kholia/Easy-Beacons-STEM/Amplified-WSPR-Beacon-v3/info/KK81.png

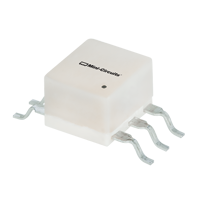
Amplified-WSPR-Beacon-v3/info/KK81.png
