kholia/Easy-Beacons-STEM/Amplified-WSPR-Beacon-v3/info/Screenshot_2022-12-17_13-03-08.png

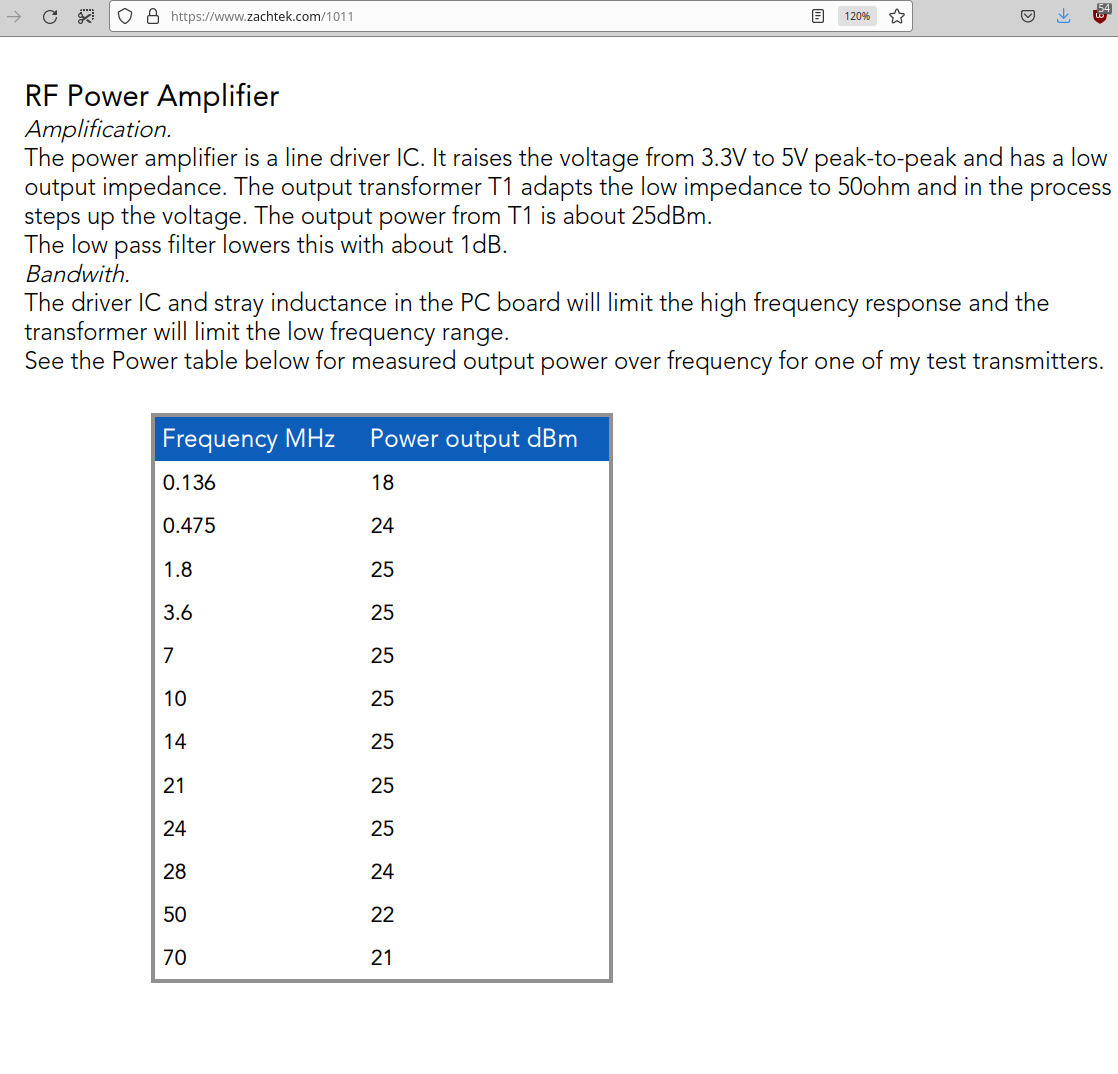
Amplified-WSPR-Beacon-v3/info/Screenshot_2022-12-17_13-03-08.png
