kholia/Easy-Beacons-STEM/Amplified-WSPR-Beacon-v3/info/Screenshot_2023-01-06_15-30-46.png

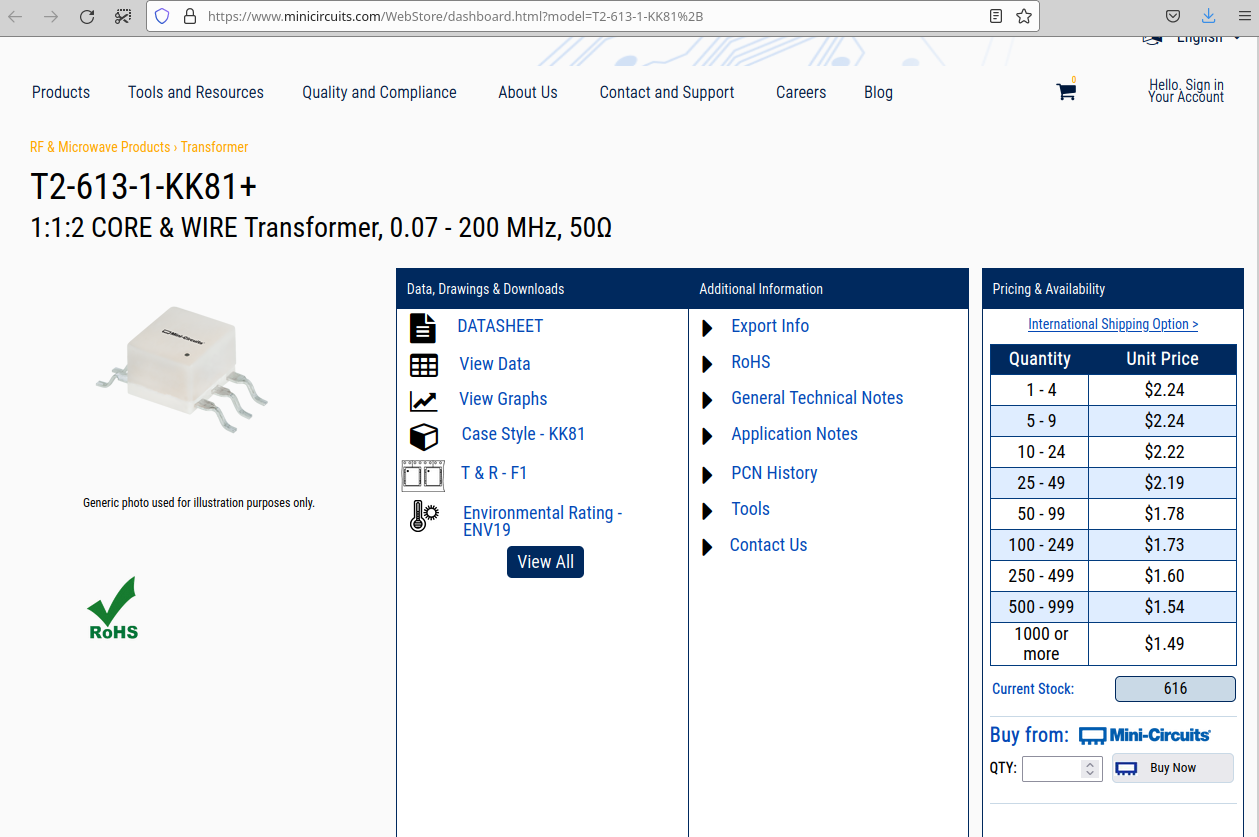
Amplified-WSPR-Beacon-v3/info/Screenshot_2023-01-06_15-30-46.png
