kholia/Easy-Beacons-STEM/Amplified-WSPR-Beacon-v3/info/WSPR Desktop Open small.jpg

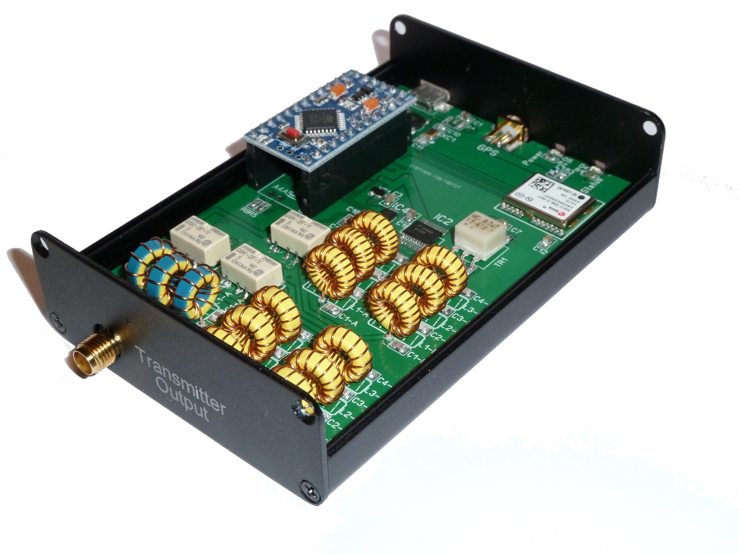
Amplified-WSPR-Beacon-v3/info/WSPR Desktop Open small.jpg
