kholia/Easy-Beacons-STEM/Amplified-WSPR-Beacon/Home-RX-Park-TX-Screenshot_2022-10-17_21-01-00.png

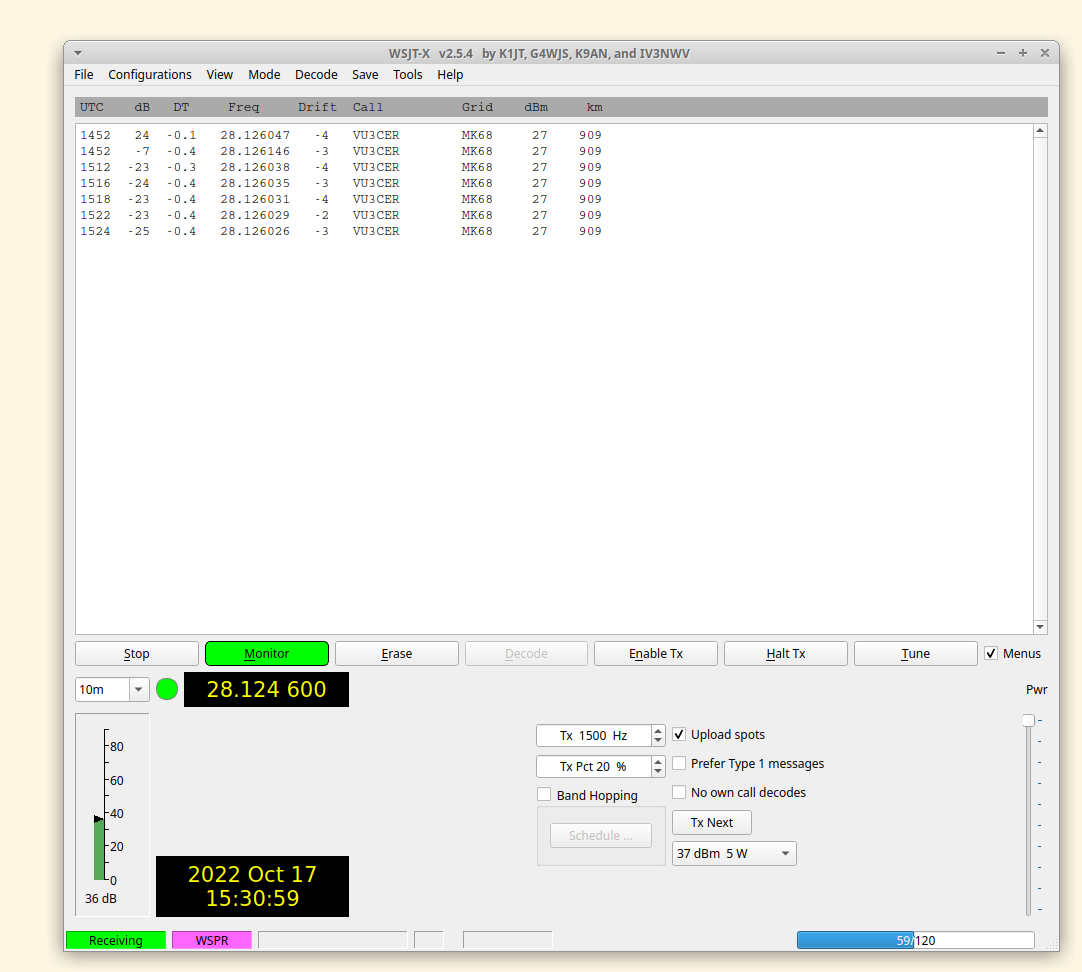
Amplified-WSPR-Beacon/Home-RX-Park-TX-Screenshot_2022-10-17_21-01-00.png
