kholia/Easy-Beacons-STEM/Amplified-WSPR-Beacon/Same-7.4v-Screenshot_2022-10-18_15-10-08.png

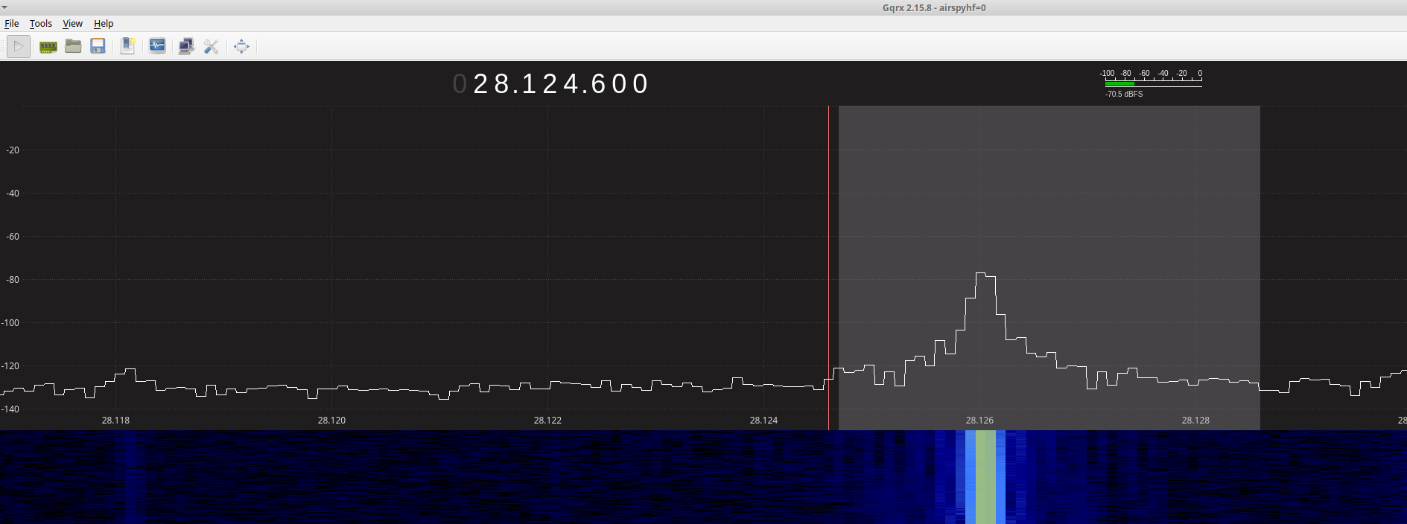
Amplified-WSPR-Beacon/Same-7.4v-Screenshot_2022-10-18_15-10-08.png
