kholia/Easy-Beacons-STEM/Amplified-WSPR-Beacon/Screenshot_2022-10-17_15-22-22.png

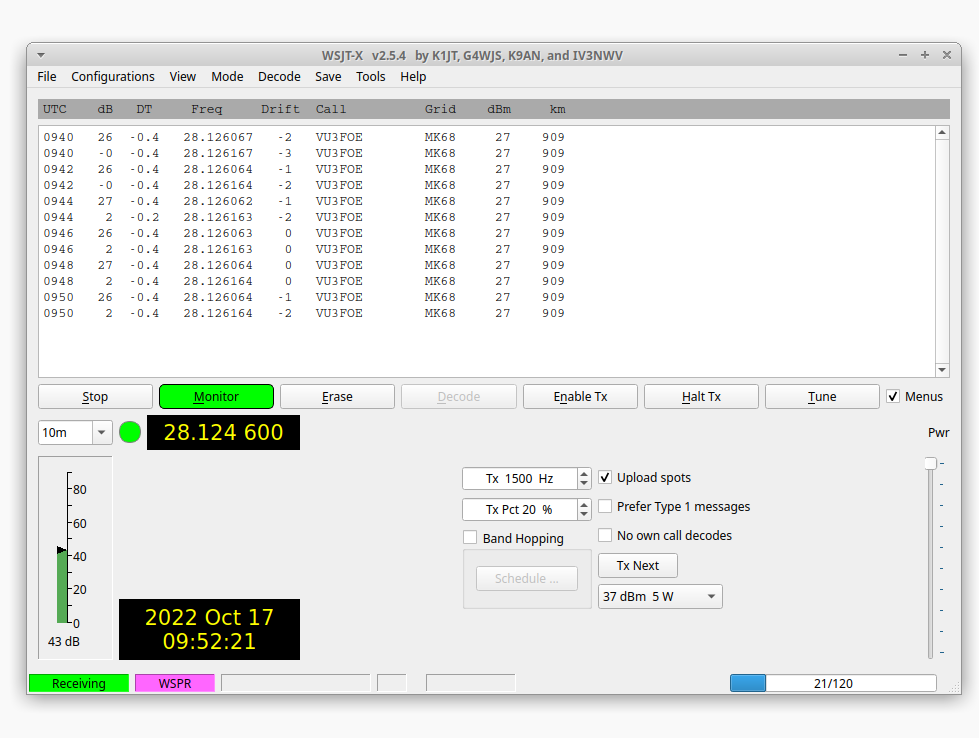
Amplified-WSPR-Beacon/Screenshot_2022-10-17_15-22-22.png
