kholia/Easy-Beacons-STEM/Amplified-WSPR-Beacon/Screenshot_2022-10-17_15-31-09.png

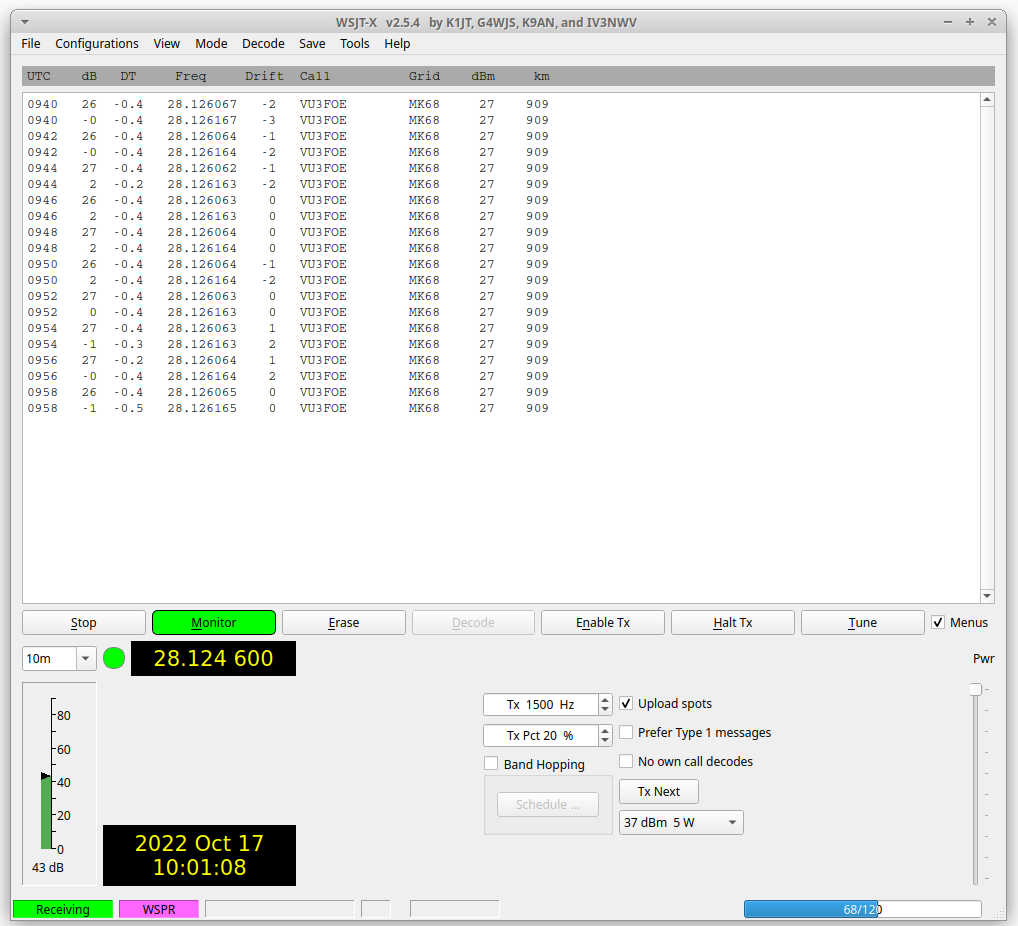
Amplified-WSPR-Beacon/Screenshot_2022-10-17_15-31-09.png
