kholia/Easy-Beacons-STEM/Amplified-WSPR-Beacon/Screenshot_2022-10-19_18-15-18.png

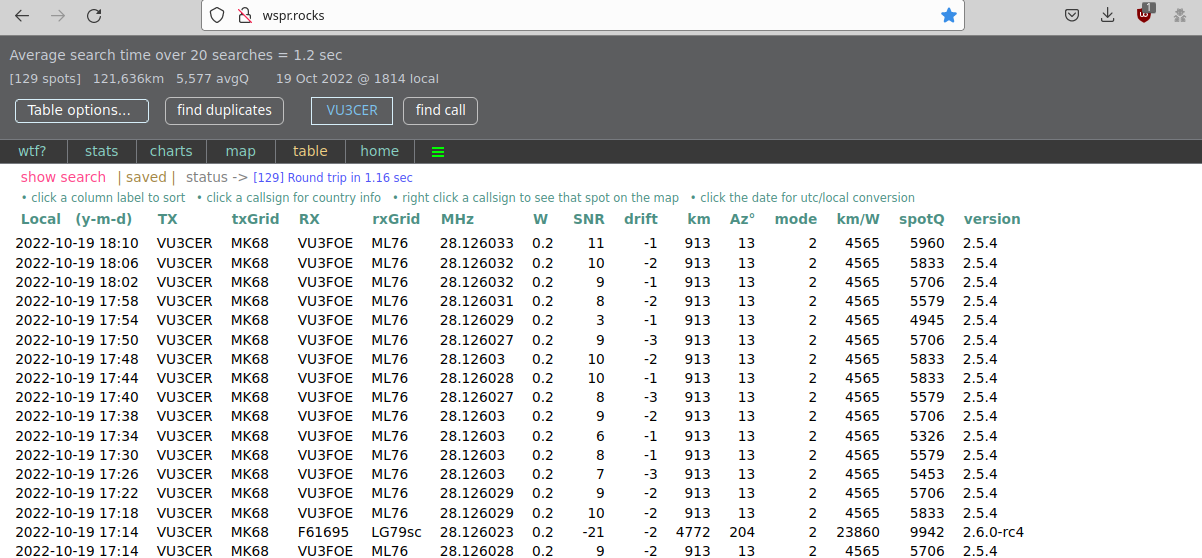
Amplified-WSPR-Beacon/Screenshot_2022-10-19_18-15-18.png
