kholia/Easy-Beacons-STEM/Amplified-WSPR-Beacon/Screenshot_2022-10-19_19-35-20.png

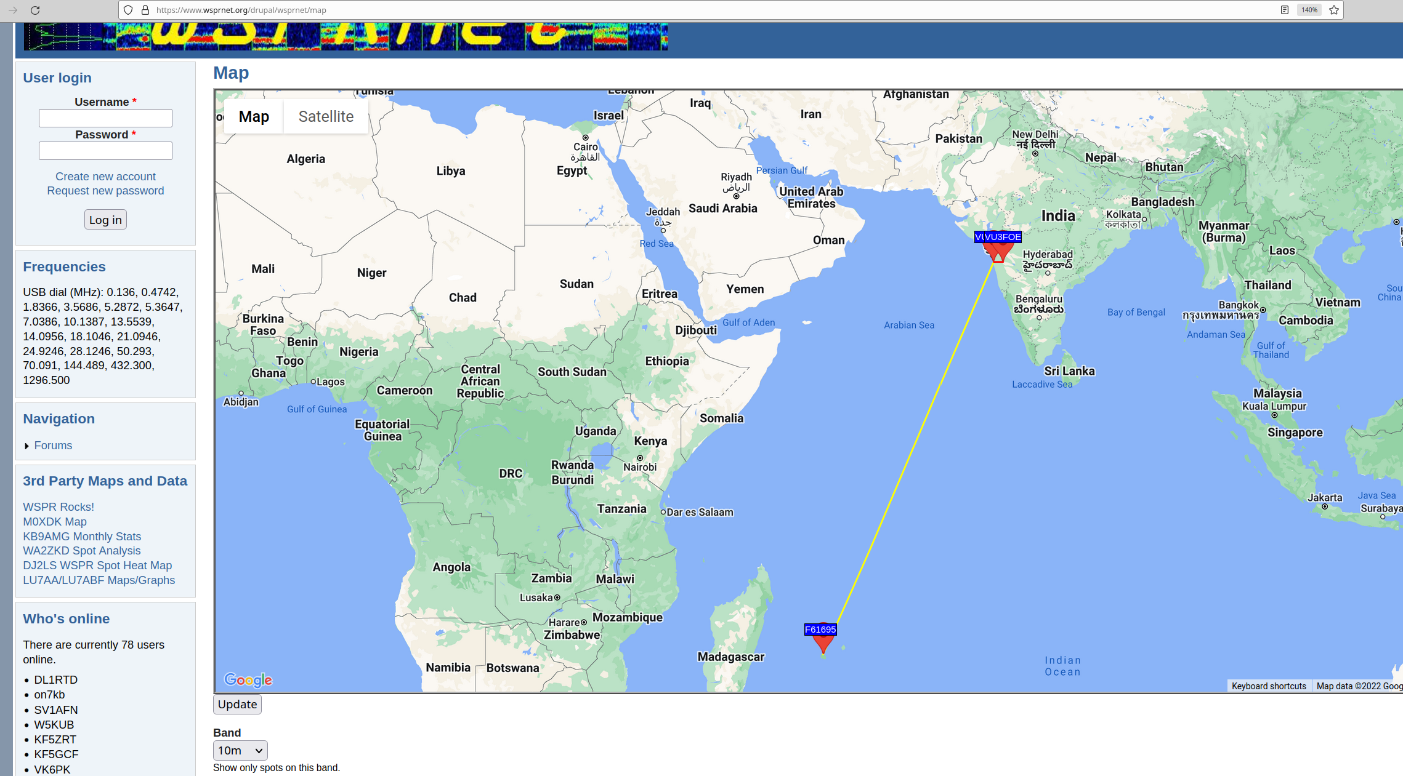
Amplified-WSPR-Beacon/Screenshot_2022-10-19_19-35-20.png
