kholia/Easy-Beacons-STEM/Amplified-WSPR-Beacon/Screenshot_2022-10-24_17-50-40.png

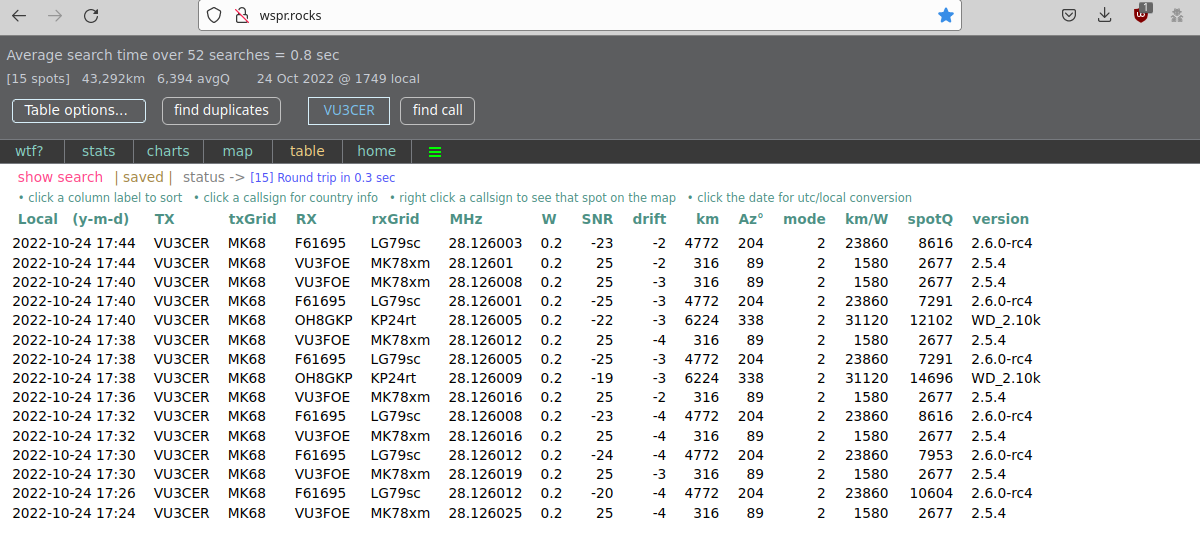
Amplified-WSPR-Beacon/Screenshot_2022-10-24_17-50-40.png
