kholia/Easy-Beacons-STEM/Amplified-WSPR-Beacon/Screenshot_2022-10-24_18-13-15.png

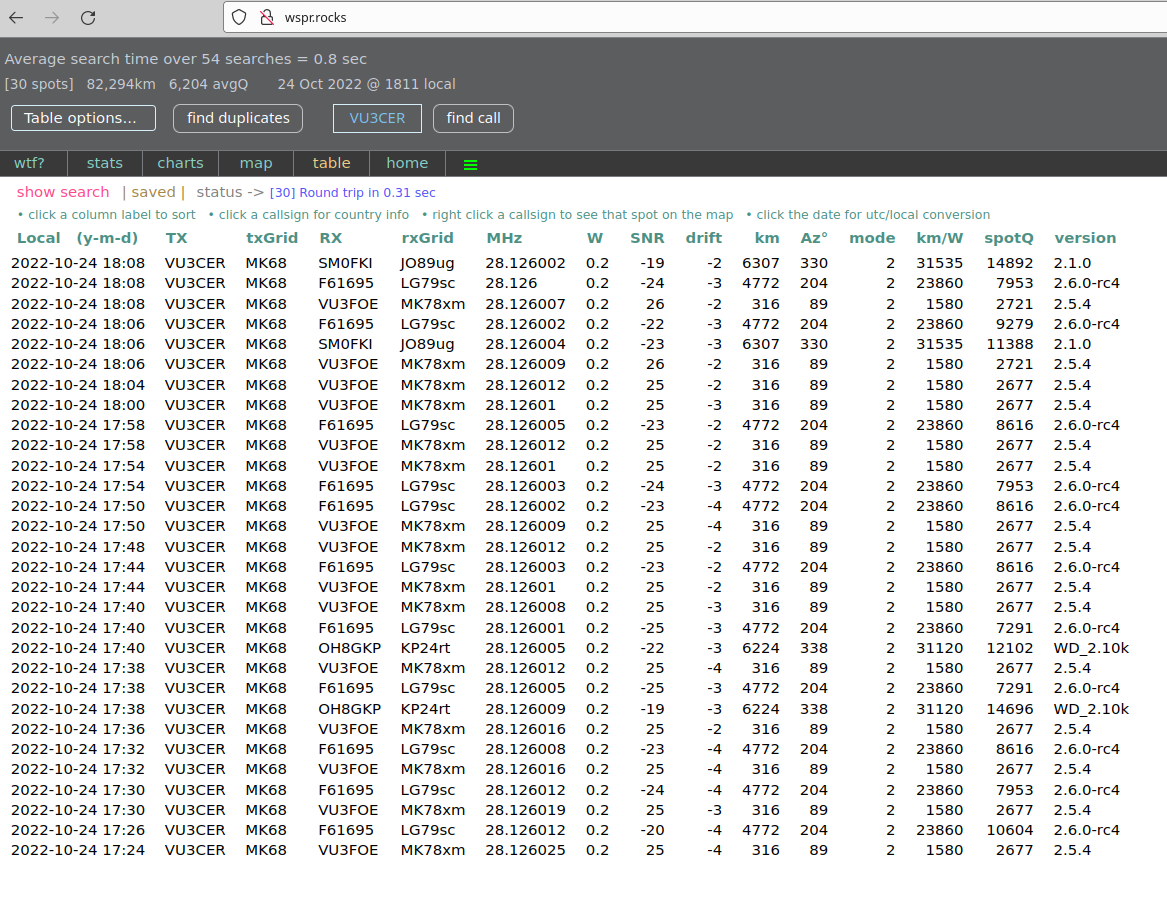
Amplified-WSPR-Beacon/Screenshot_2022-10-24_18-13-15.png
