kholia/Easy-Beacons-STEM/Amplified-WSPR-Beacon/Screenshot_2022-10-24_18-23-26.png

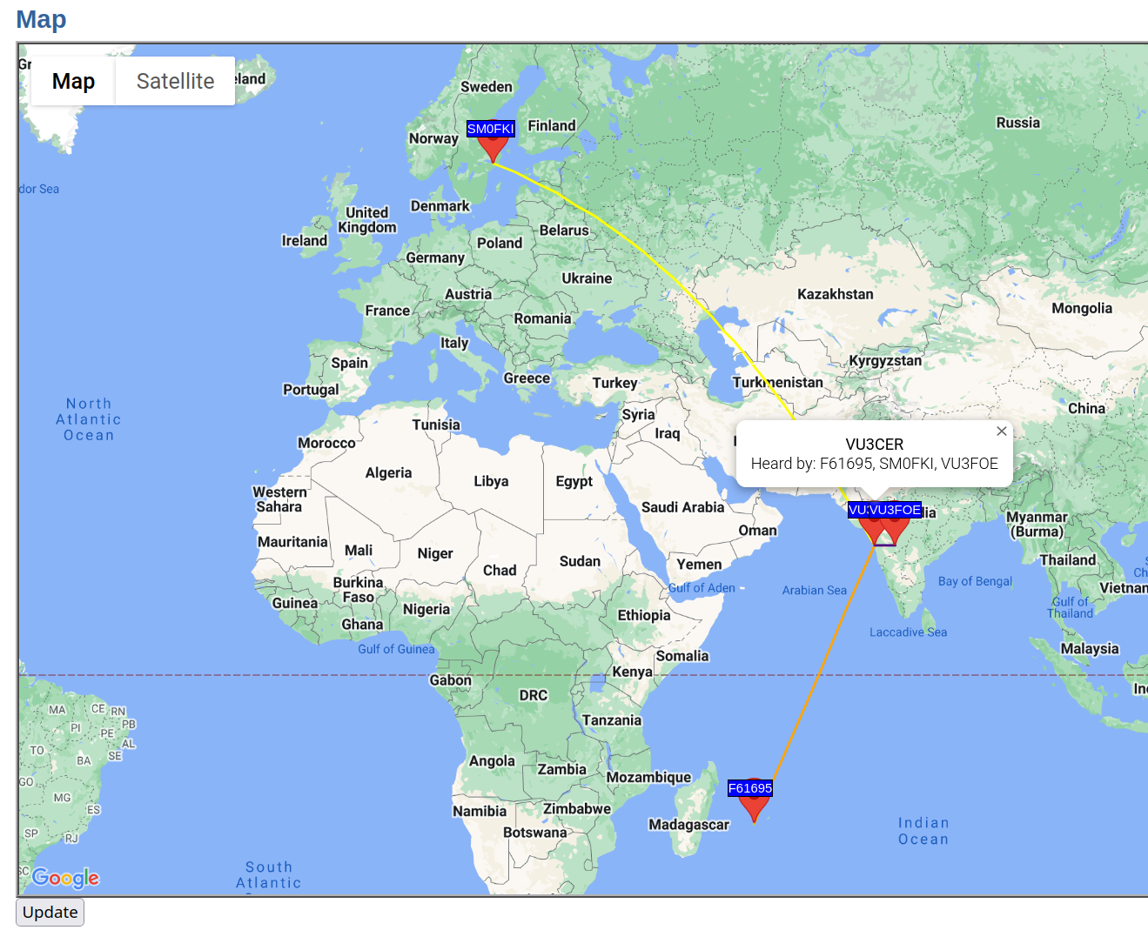
Amplified-WSPR-Beacon/Screenshot_2022-10-24_18-23-26.png
