kholia/Easy-Beacons-STEM/Amplified-WSPR-Beacon/Screenshot_2022-10-24_19-00-13.png

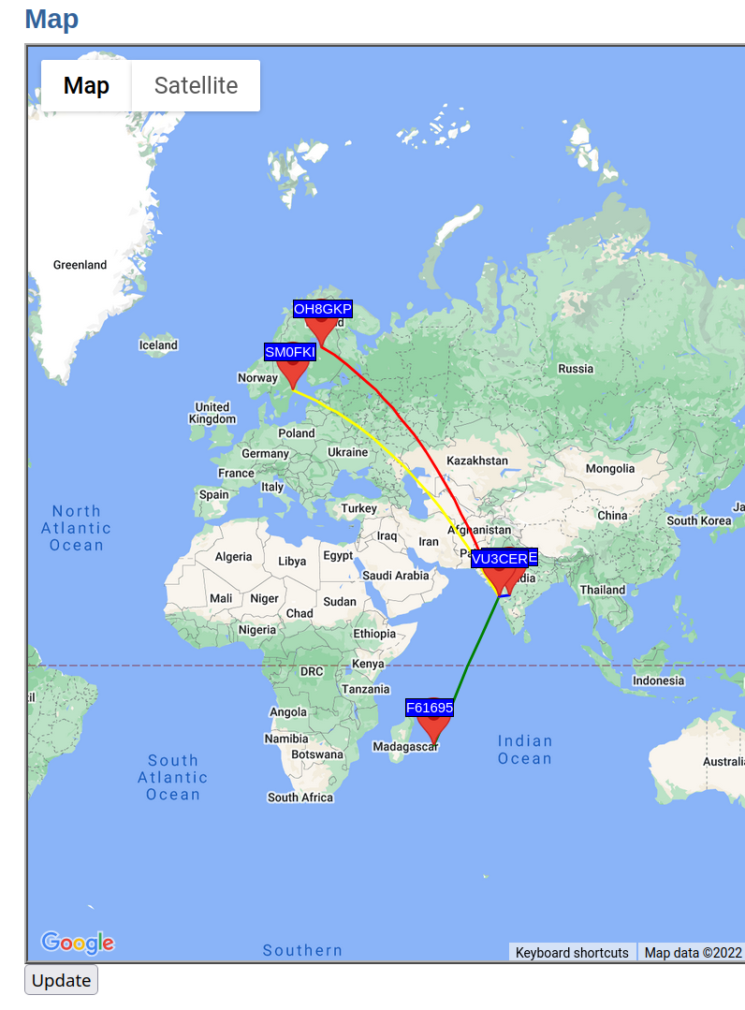
Amplified-WSPR-Beacon/Screenshot_2022-10-24_19-00-13.png
