kholia/Easy-Beacons-STEM/Amplified-WSPR-Beacon/With-Amplifier-5-Feet-Away-9.4v-Screenshot_2022-10-18_15-08-47.png

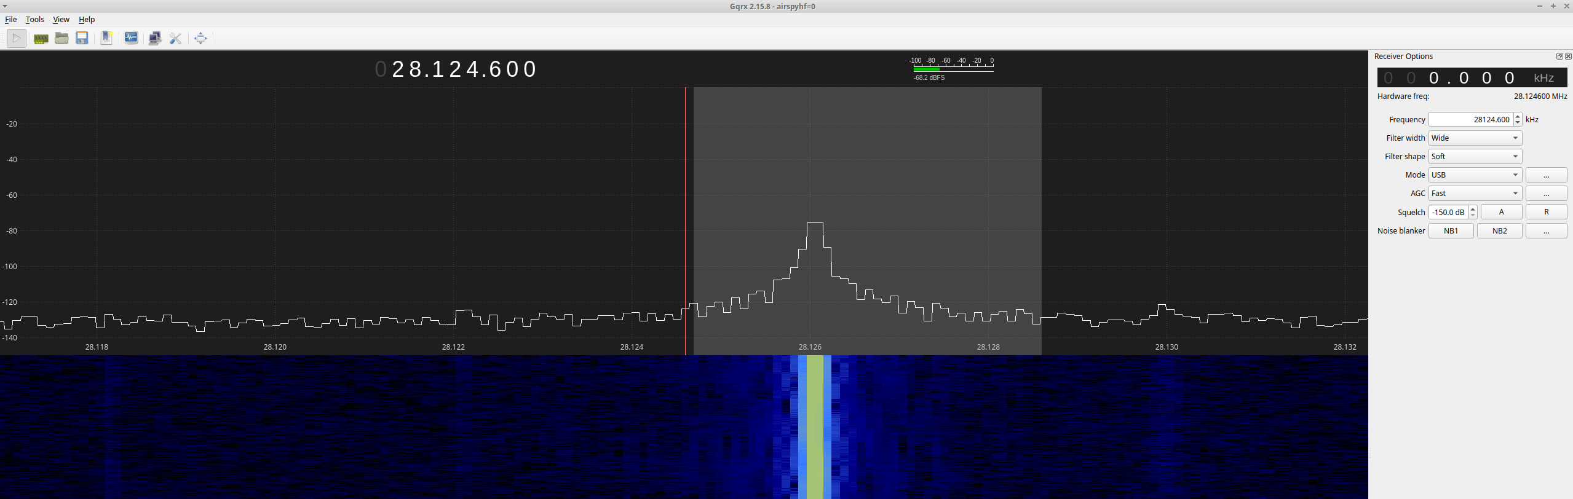
Amplified-WSPR-Beacon/With-Amplifier-5-Feet-Away-9.4v-Screenshot_2022-10-18_15-08-47.png
