kholia/Easy-Beacons-STEM/Amplified-WSPR-Beacon/Without-Amplifier-Screenshot_2022-10-18_15-14-42.png

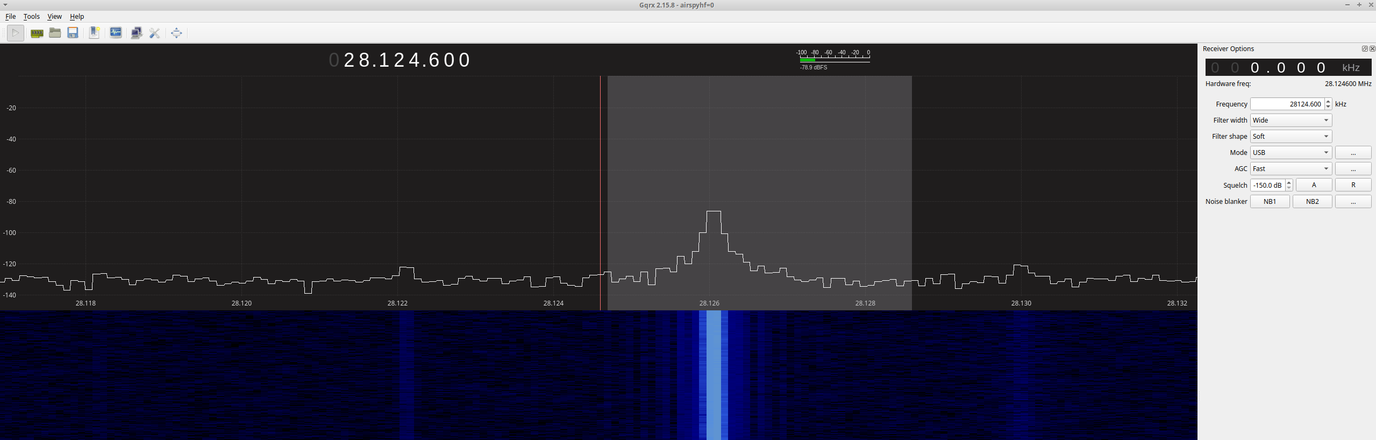
Amplified-WSPR-Beacon/Without-Amplifier-Screenshot_2022-10-18_15-14-42.png
