kholia/Easy-Beacons-STEM/datasheets/Screenshot_2022-12-05_10-16-25.png

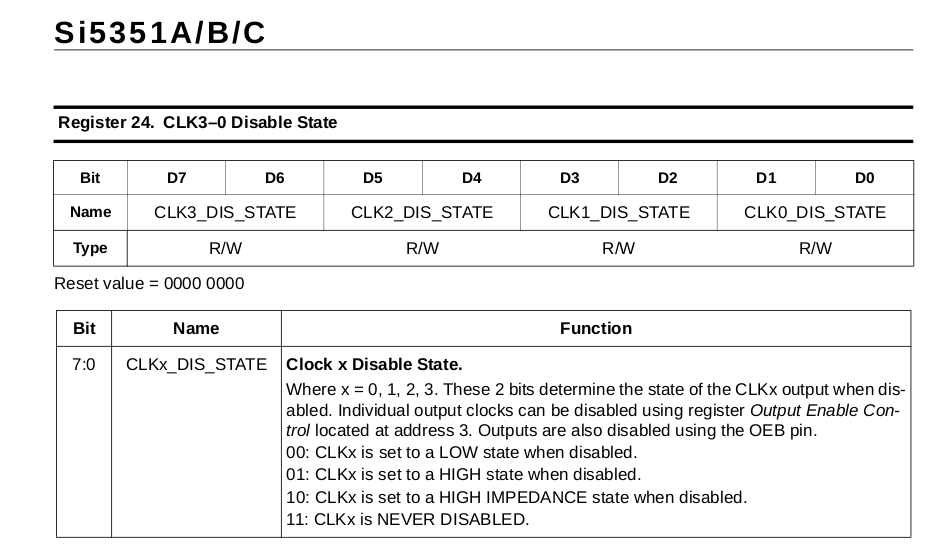
datasheets/Screenshot_2022-12-05_10-16-25.png
