kholia/Easy-Beacons-STEM/Shortcut-LPF/Screenshot_2022-10-17_18-11-42.png

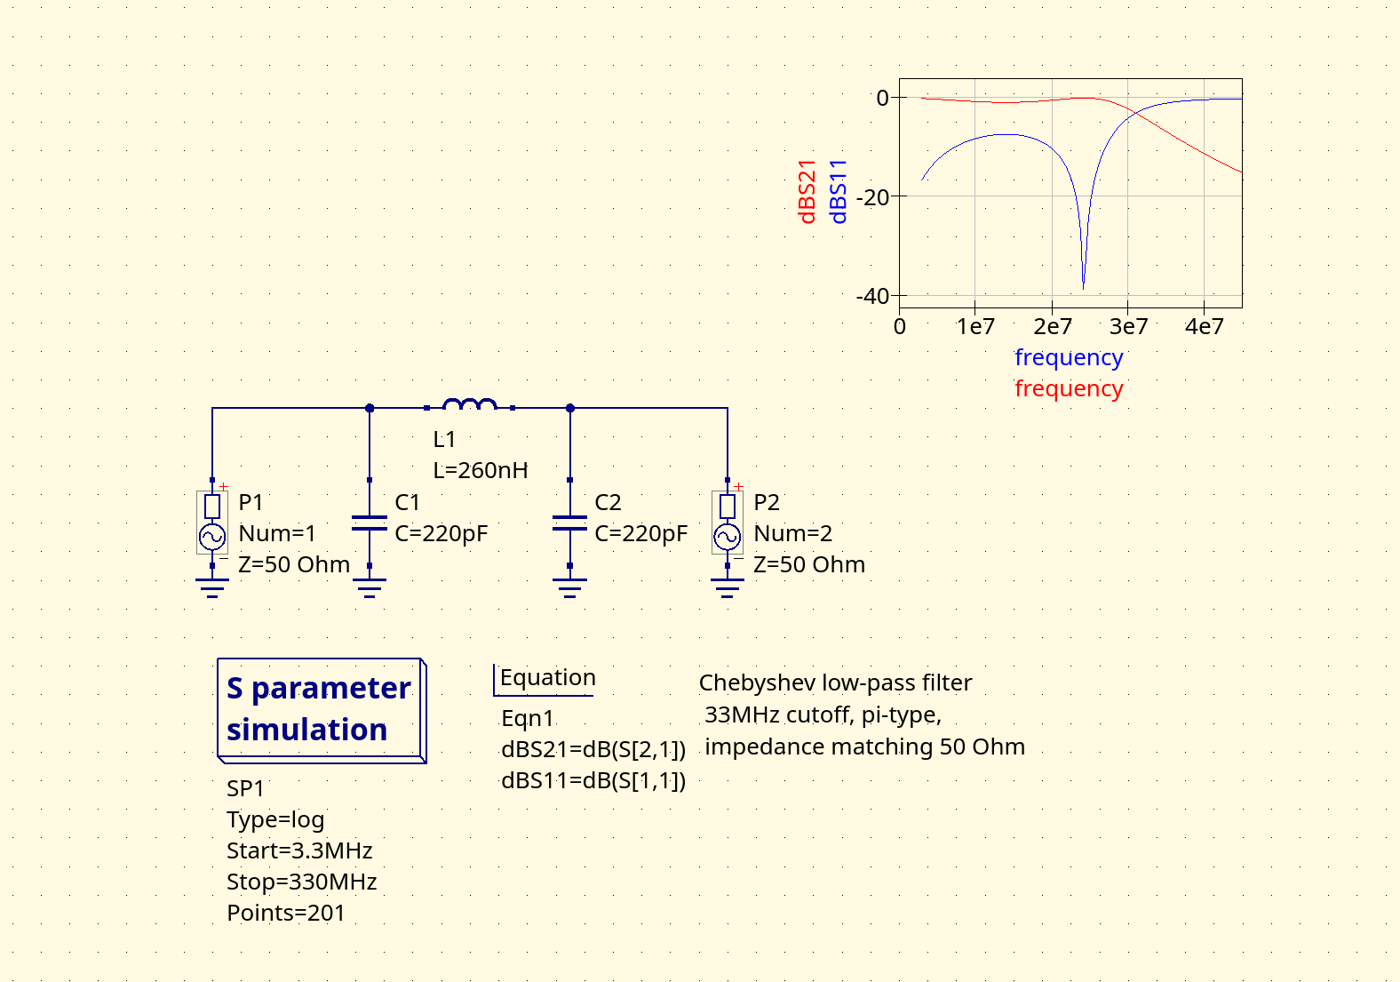
Shortcut-LPF/Screenshot_2022-10-17_18-11-42.png
