kholia/Easy-Beacons-STEM/Shortcut-LPF/Screenshot_2022-10-17_18-12-13.png

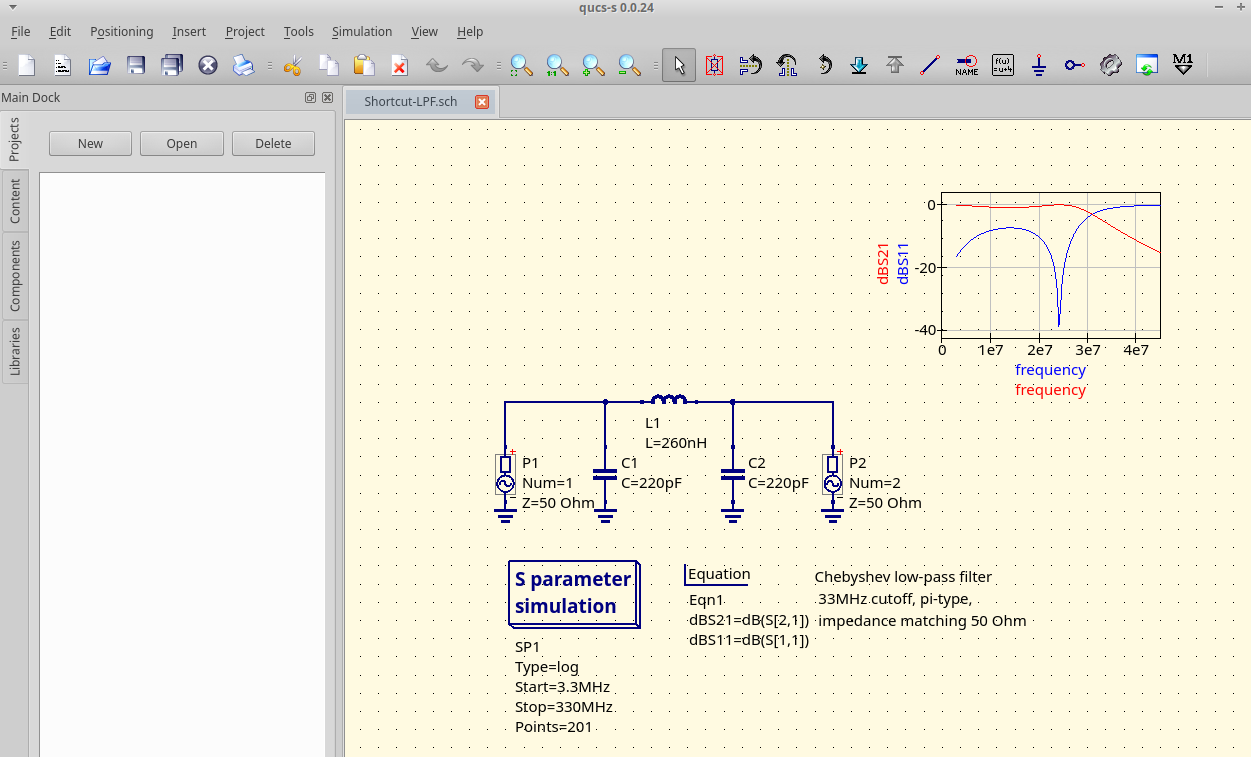
Shortcut-LPF/Screenshot_2022-10-17_18-12-13.png
