kholia/Easy-Beacons-STEM/Amplified-WSPR-Beacon/models/N0016A.stp

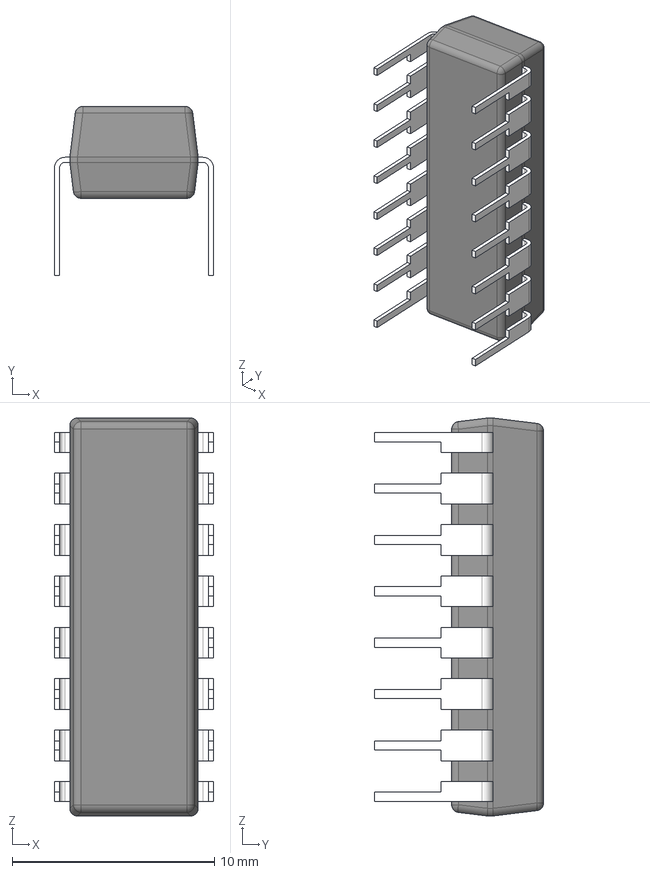
[picture p57: CAD file, 2023-01-08]
Amplified-WSPR-Beacon/models/N0016A.stp
7.87 x 8.37 x 19.7 mm
BODY_N0016A_AF0
LEAD_N0016A_AF1
LEAD_N0016A x 10
LEAD_N0016A_AF3
LEAD_N0016A_AF5
LEAD_N0016A_AF0
LEAD_N0016A_AF2
LEAD_N0016A_AF4
