kholia/Easy-Beacons-STEM/Amplified-WSPR-Beacon/models/pj-307.step

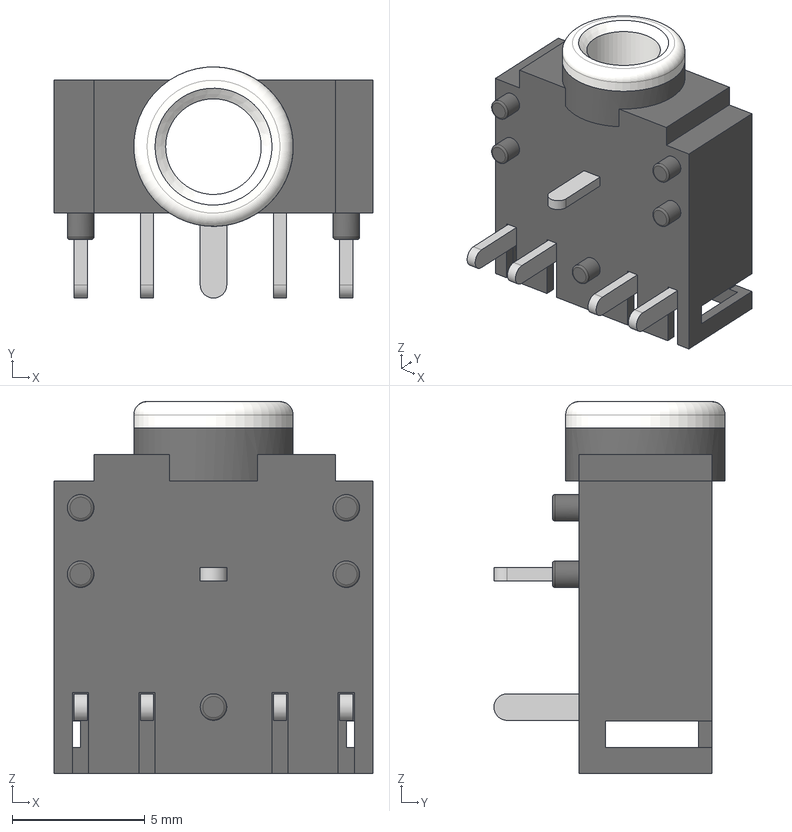
[picture p58: CAD file, 2023-01-08]
Amplified-WSPR-Beacon/models/pj-307.step
12.0 x 8.70 x 14.0 mm
