kholia/Easy-Beacons-STEM/Amplified-WSPR-Beacon/models/24DR.STEP

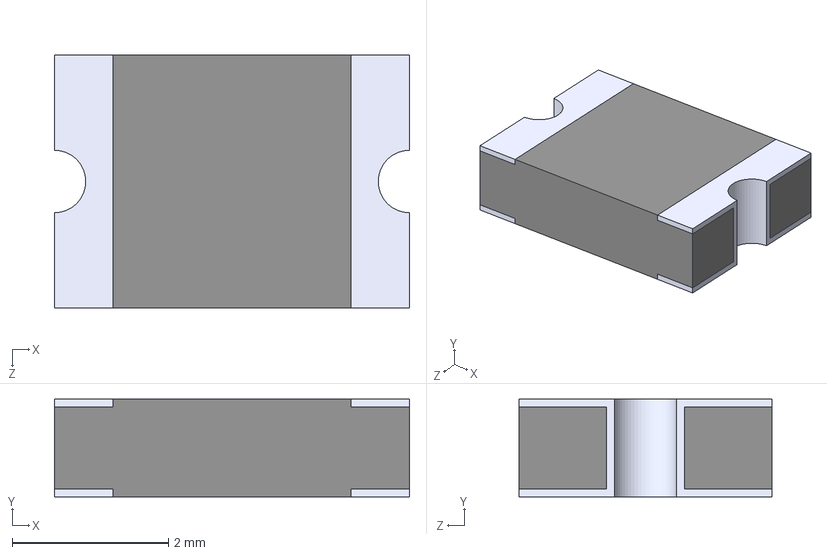
[picture p59: CAD file, 2023-01-08]
Amplified-WSPR-Beacon/models/24DR.STEP
4.55 x 1.25 x 3.24 mm
