kholia/Easy-Beacons-STEM/Amplified-WSPR-Beacon/models/User Library-TO-92-2_54-line.STEP

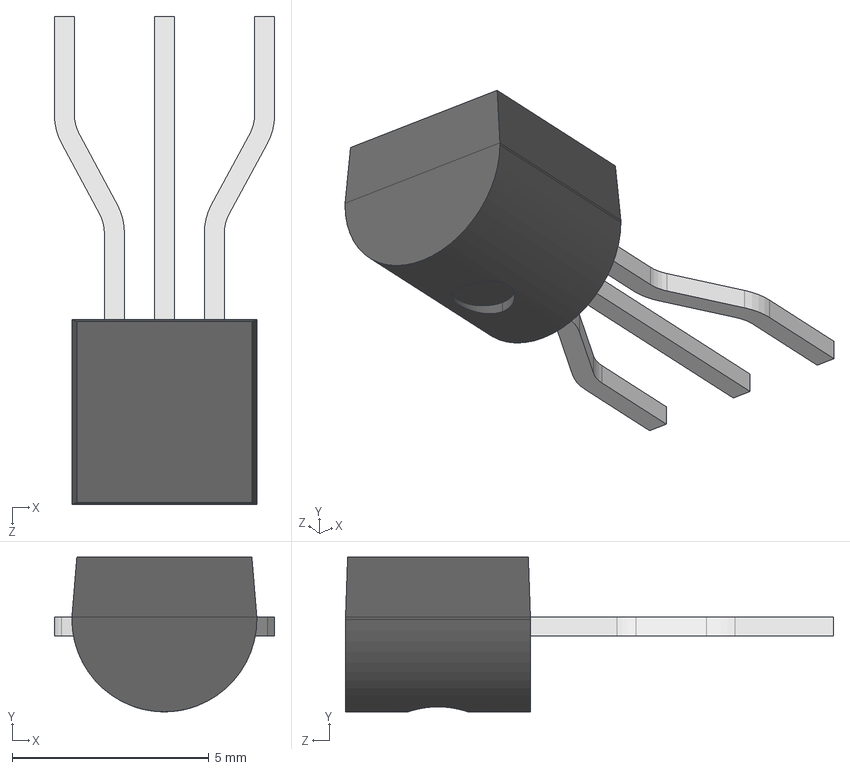
[picture p60: CAD file, 2023-01-08]
Amplified-WSPR-Beacon/models/User Library-TO-92-2_54-line.STEP
5.60 x 3.93 x 12.4 mm
User Library-TO-92 Version2_TO-92 Part1
User Library-TO-92 Version2_TO-92 Part3
User Library-TO-92 Version2_TO-92 Part4
User Library-TO-92 Version2_TO-92 Part5
