kholia/Easy-Beacons-STEM/QRPp-Amplifier-v2/QRPp-Amplifier-v2.pdf

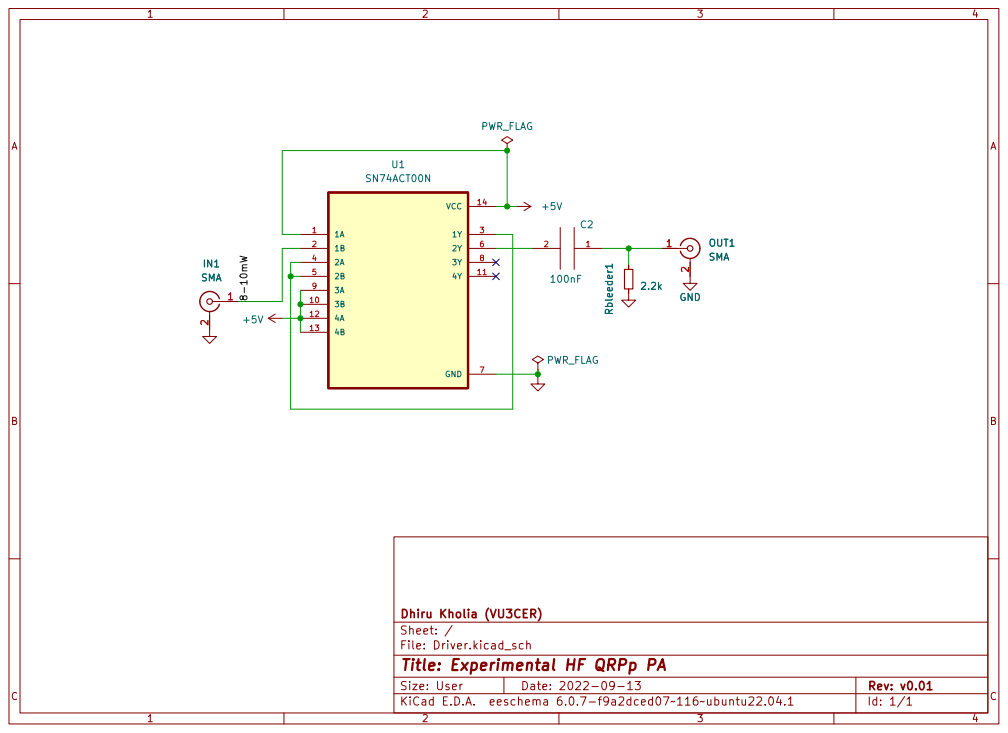
[picture p67: page 1]

File: Driver.kicad_sch Sheet: / Dhiru Kholia (VU3CER)

Id: 1/1 Title: Experimental HF QRPp PA
