kholia/Easy-Beacons-STEM/Amplified-WSPR-Beacon/Simulation/BS170-Driver.asc

C1: cap; 100nF
C4: cap; 100nF
L2: ind; 470µH
M2: nmos; BS170
R1: res; 50
V1: voltage; PULSE(0 5 0 0.1p 0.1p 35ns 70ns)
V2: voltage; 29
V3: voltage; 11.1
Named nets: W1, 0, Vp, Vb
.lib bs170.lib
.tran 2500us
35ns 70ns  <-> 71ns 142ns
