kholia/Easy-Beacons-STEM/Amplified-WSPR-Beacon/Simulation/IRF510-Sample.asc

C1: cap; 100nF
C4: cap; 100nF
L2: ind; 47µH
R1: res; 50
U1: irf510
V1: voltage; PULSE(0 5 0 0.1p 0.1p 35ns 70ns)
V3: voltage; 8
Named nets: W1, 0, Vb
.lib bs170.lib
.tran 250us
35ns 70ns  <-> 71ns 142ns
